TLShuang/PG16/PCB/PCBPlates_v17.sch

## EAGLE design PCB/PCBPlates_v17.sch (2025-01-23)

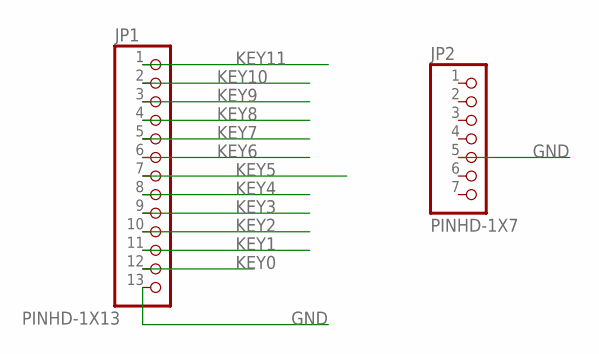
[picture p7: schematic PCBPlates_v17.sch]

Parts:
JP1: PINHD-1X13; 1X13
JP2: PINHD-1X7; 1X07

Connections:
GND: JP1.13, JP2.5
KEY0: JP1.12
KEY1: JP1.11
KEY2: JP1.10
KEY3: JP1.9
KEY4: JP1.8
KEY5: JP1.7
KEY6: JP1.6
KEY7: JP1.5
KEY8: JP1.4
KEY9: JP1.3
KEY10: JP1.2
KEY11: JP1.1
